PassarinhoAzul/Grupo-2-Projeto-Bixo-GER/entrega2/esquemático/arquivos_kicad/esquematico.kicad_sch

## KiCad design entrega2/esquemático/arquivos_kicad/esquematico.kicad_sch (2026-07-09)

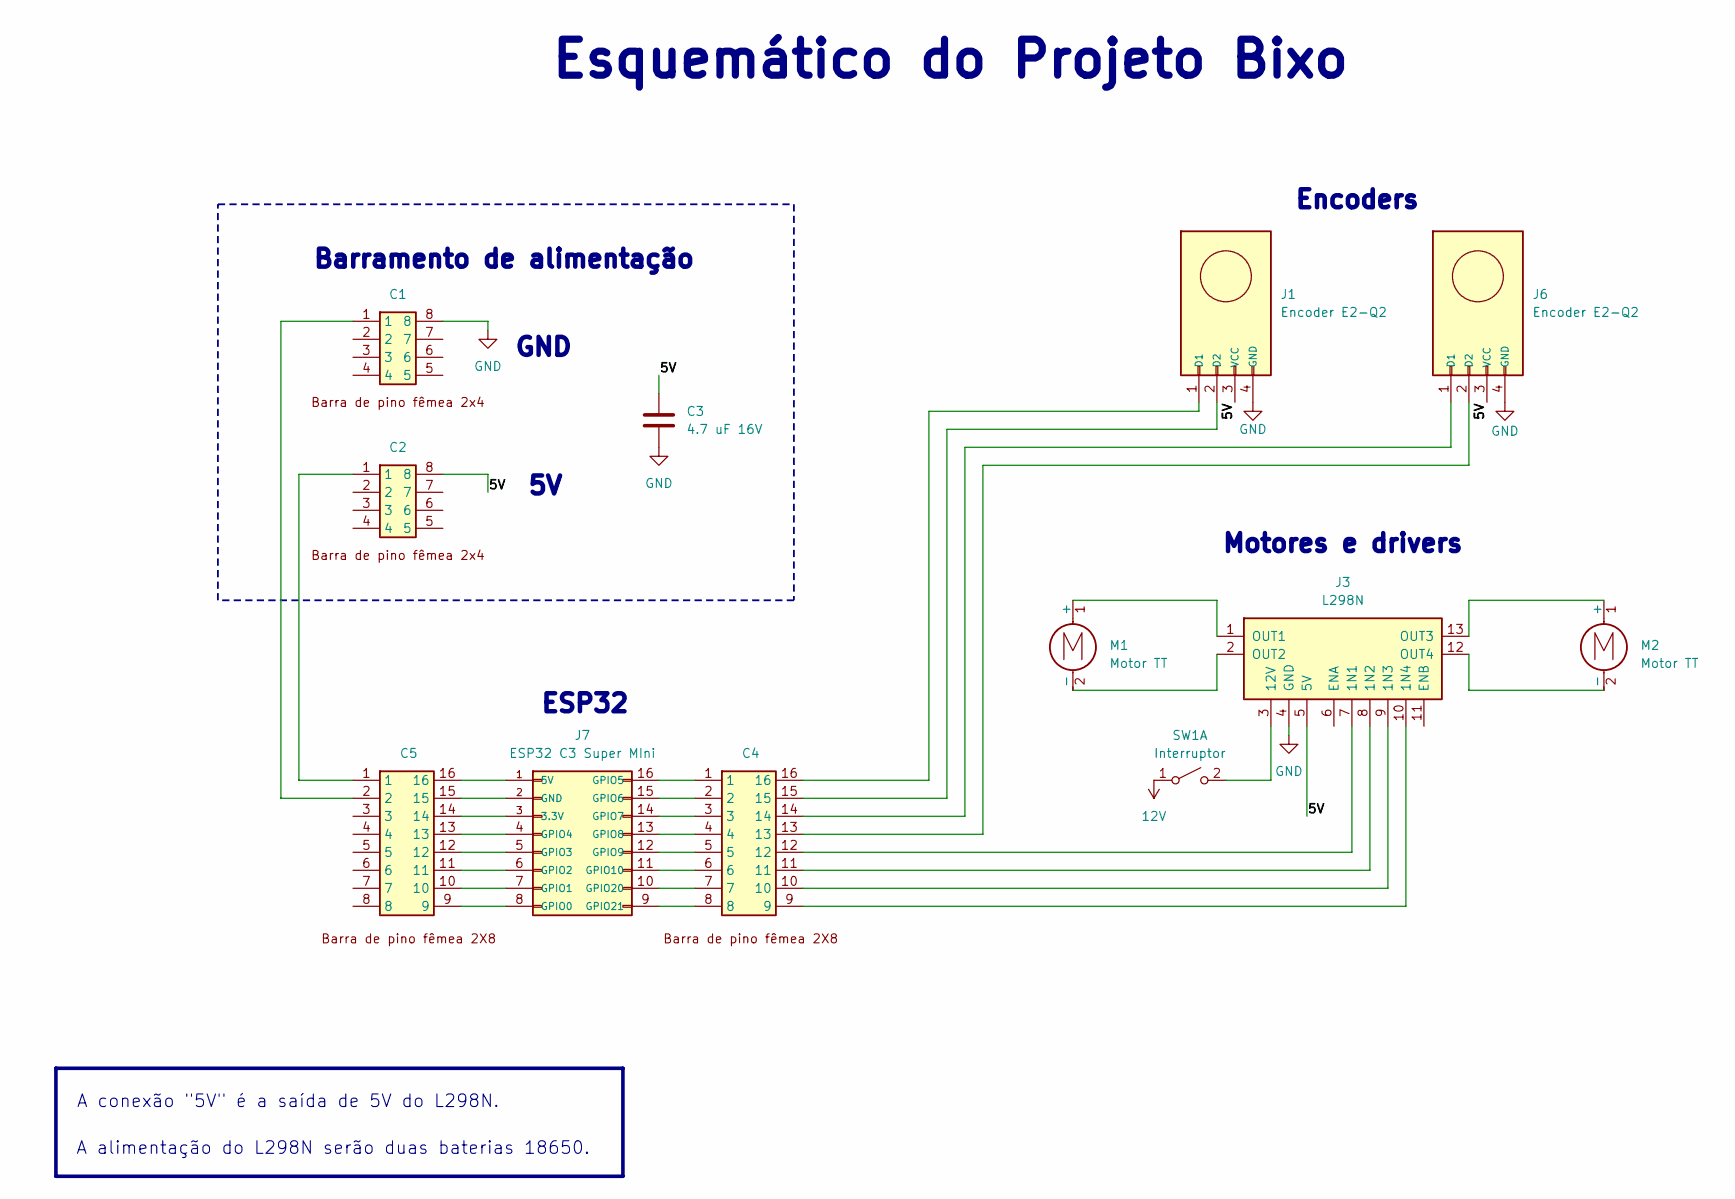
[picture p24: schematic esquematico.kicad_sch]

Parts:
C1, C2, C4, C5: (no value)
C3: 4.7 uF 16V
J1, J6: Encoder E2-Q2
J3: L298N
J7: ESP32 C3 Super MIni
M1, M2: Motor TT
SW1: Interruptor

Connections:
5V: C2.8, C3.1, J1.3 (VCC), J3.5 (5V), J6.3 (VCC)
12V: SW1.1 (A)
GND: C1.8, C3.2, J1.4 (GND), J3.4 (GND), J6.4 (GND)
unnamed: C1.1, C5.2
unnamed: C2.1, C5.1
unnamed: C4.1, J7.16 (GPIO5)
unnamed: C4.2, J7.15 (GPIO6)
unnamed: C4.3, J7.14 (GPIO7)
unnamed: C4.4, J7.13 (GPIO8)
unnamed: C4.5, J7.12 (GPIO9)
unnamed: C4.6, J7.11 (GPIO10)
unnamed: C4.7, J7.10 (GPIO20)
unnamed: C4.8, J7.9 (GPIO21)
unnamed: C4.9, J3.10 (1N4)
unnamed: C4.10, J3.9 (1N3)
unnamed: C4.11, J3.8 (1N2)
unnamed: C4.12, J3.7 (1N1)
unnamed: C4.13, J6.2 (D2)
unnamed: C4.14, J6.1 (D1)
unnamed: C4.15, J1.2 (D2)
unnamed: C4.16, J1.1 (D1)
unnamed: C5.9, J7.8 (GPIO0)
unnamed: C5.10, J7.7 (GPIO1)
unnamed: C5.11, J7.6 (GPIO2)
unnamed: C5.12, J7.5 (GPIO3)
unnamed: C5.13, J7.4 (GPIO4)
unnamed: C5.14, J7.3 (3.3V)
unnamed: C5.15, J7.2 (GND)
unnamed: C5.16, J7.1 (5V)
unnamed: J3.1 (OUT1), M1.1 (+)
unnamed: J3.2 (OUT2), M1.2 (-)
unnamed: J3.3 (12V), SW1.2 (B)
unnamed: J3.12 (OUT4), M2.2 (-)
unnamed: J3.13 (OUT3), M2.1 (+)

Notes on the sheet:
A alimentação do L298N serão duas baterias 18650.
Barramento de alimentação
Encoders
Esquemático do Projeto Bixo
GND
ESP32
Motores e drivers
A conexão "5V" é a saída de 5V do L298N.
