PassarinhoAzul/Grupo-2-Projeto-Bixo-GER/entrega2/esquemático/biblioteca_kicad/esquematico.kicad_sch

## KiCad design entrega2/esquemático/biblioteca_kicad/esquematico.kicad_sch (2026-07-01)

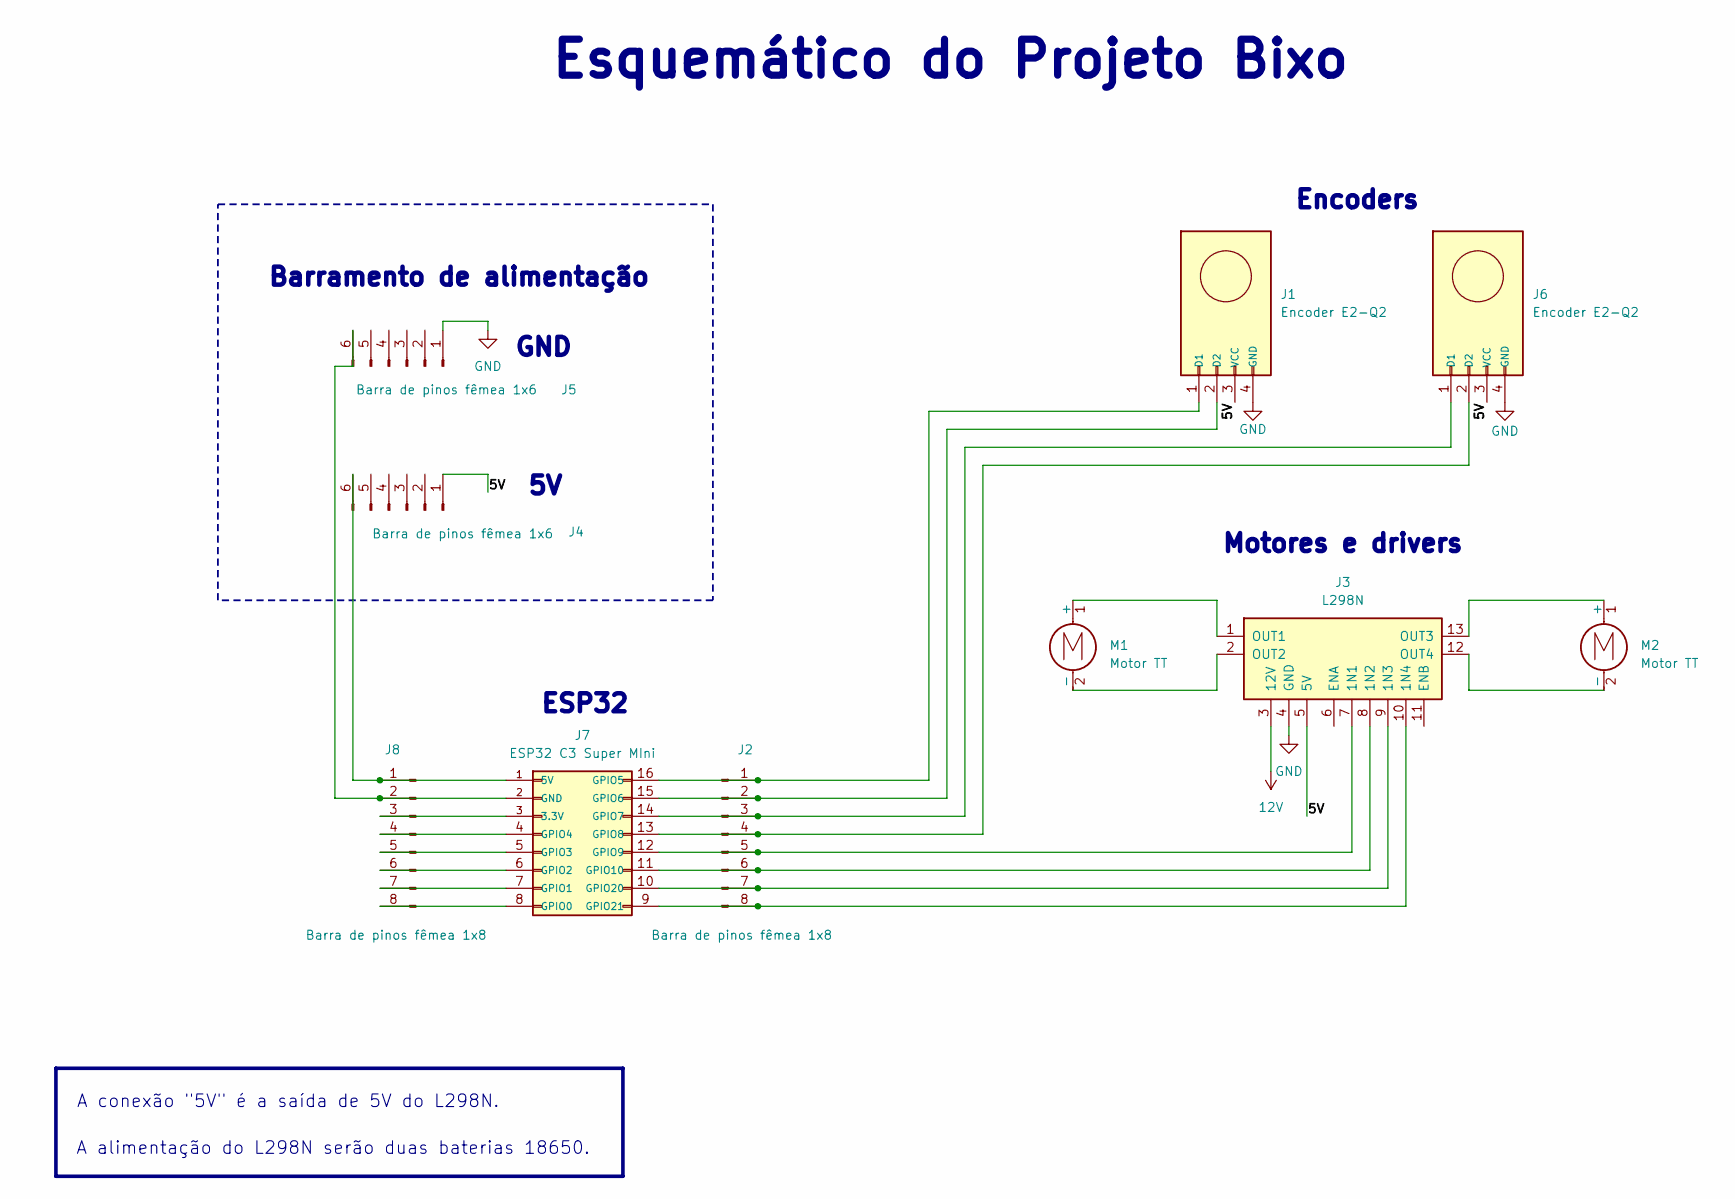
[picture p25: schematic esquematico.kicad_sch]

Parts:
J1, J6: Encoder E2-Q2
J2, J8: Barra de pinos fêmea 1x8
J3: L298N
J4, J5: Barra de pinos fêmea 1x6
J7: ESP32 C3 Super MIni
M1, M2: Motor TT

Connections:
5V: J1.3 (VCC), J3.5 (5V), J4.1, J6.3 (VCC)
12V: J3.3 (12V)
GND: J1.4 (GND), J3.4 (GND), J5.1, J6.4 (GND)
unnamed: J1.1 (D1), J2.1, J7.16 (GPIO5)
unnamed: J1.2 (D2), J2.2, J7.15 (GPIO6)
unnamed: J2.3, J6.1 (D1), J7.14 (GPIO7)
unnamed: J2.4, J6.2 (D2), J7.13 (GPIO8)
unnamed: J2.5, J3.7 (1N1), J7.12 (GPIO9)
unnamed: J2.6, J3.8 (1N2), J7.11 (GPIO10)
unnamed: J2.7, J3.9 (1N3), J7.10 (GPIO20)
unnamed: J2.8, J3.10 (1N4), J7.9 (GPIO21)
unnamed: J3.1 (OUT1), M1.1 (+)
unnamed: J3.2 (OUT2), M1.2 (-)
unnamed: J3.12 (OUT4), M2.2 (-)
unnamed: J3.13 (OUT3), M2.1 (+)
unnamed: J4.6, J7.1 (5V), J8.1
unnamed: J5.6, J7.2 (GND), J8.2
unnamed: J7.3 (3.3V), J8.3
unnamed: J7.4 (GPIO4), J8.4
unnamed: J7.5 (GPIO3), J8.5
unnamed: J7.6 (GPIO2), J8.6
unnamed: J7.7 (GPIO1), J8.7
unnamed: J7.8 (GPIO0), J8.8

Notes on the sheet:
A alimentação do L298N serão duas baterias 18650.
Barramento de alimentação
Encoders
Esquemático do Projeto Bixo
GND
ESP32
Motores e drivers
A conexão "5V" é a saída de 5V do L298N.
